OSHE-Github/Chatter-Cuffs/walkie-talkie/src/config.cpp

#include "config.h"

// In case each transport packet needs to start with a specific header, define transport_header here.
// TRANSPORT_HEADER_SIZE needs to be defined in config.h
// For example, when TRANSPORT_HEADER_SIZE is defined as 3,  define transport_header for example as {0x1F, 0xCD, 0x01};
uint8_t transport_header[TRANSPORT_HEADER_SIZE] = {};


// i2s config for using the internal ADC
#if CONFIG_IDF_TARGET_ESP32
i2s_config_t i2s_adc_config = {
    .mode = (i2s_mode_t)(I2S_MODE_MASTER | I2S_MODE_RX | I2S_MODE_ADC_BUILT_IN),
    .sample_rate = SAMPLE_RATE,
    .bits_per_sample = I2S_BITS_PER_SAMPLE_16BIT,
    .channel_format = I2S_MIC_CHANNEL,
#if ESP_IDF_VERSION >= ESP_IDF_VERSION_VAL(4, 2, 0)
    .communication_format = I2S_COMM_FORMAT_STAND_MSB,
#else
    .communication_format = I2S_COMM_FORMAT_I2S_LSB,
#endif
    .intr_alloc_flags = ESP_INTR_FLAG_LEVEL1,
    .dma_buf_count = 4,
    .dma_buf_len = 64,
    .use_apll = false,
    .tx_desc_auto_clear = false,
    .fixed_mclk = 0};
#endif

// i2s config for reading from I2S
i2s_config_t i2s_mic_Config = {
    .mode = (i2s_mode_t)(I2S_MODE_MASTER | I2S_MODE_RX),
    .sample_rate = SAMPLE_RATE,
    .bits_per_sample = I2S_BITS_PER_SAMPLE_32BIT,
    .channel_format = I2S_MIC_CHANNEL,
#if ESP_IDF_VERSION >= ESP_IDF_VERSION_VAL(4, 2, 0)
    .communication_format = (i2s_comm_format_t)(I2S_COMM_FORMAT_STAND_I2S),
#else
    .communication_format = (i2s_comm_format_t)(I2S_COMM_FORMAT_I2S),
#endif
    .intr_alloc_flags = ESP_INTR_FLAG_LEVEL1,
    .dma_buf_count = 4,
    .dma_buf_len = 64,
    .use_apll = false,
    .tx_desc_auto_clear = false,
    .fixed_mclk = 0};

// i2s microphone pins
i2s_pin_config_t i2s_mic_pins = {
    .bck_io_num = I2S_MIC_SERIAL_CLOCK,
    .ws_io_num = I2S_MIC_LEFT_RIGHT_CLOCK,
    .data_out_num = I2S_PIN_NO_CHANGE,
    .data_in_num = I2S_MIC_SERIAL_DATA};

// i2s speaker pins
i2s_pin_config_t i2s_speaker_pins = {
    .bck_io_num = I2S_SPEAKER_SERIAL_CLOCK,
    .ws_io_num = I2S_SPEAKER_LEFT_RIGHT_CLOCK,
    .data_out_num = I2S_SPEAKER_SERIAL_DATA,
    .data_in_num = I2S_PIN_NO_CHANGE};
